Bowlsnapper/BSX-Mini/Photos/Hand Front.jpg

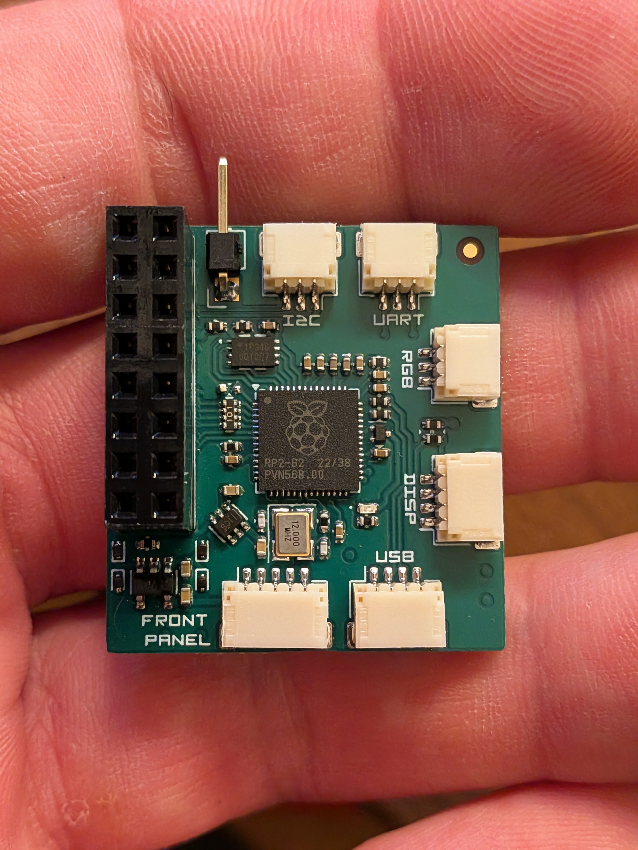
Photos/Hand Front.jpg
