Bowlsnapper/BSX-Mini/Photos/Pasted PCB 1.jpg

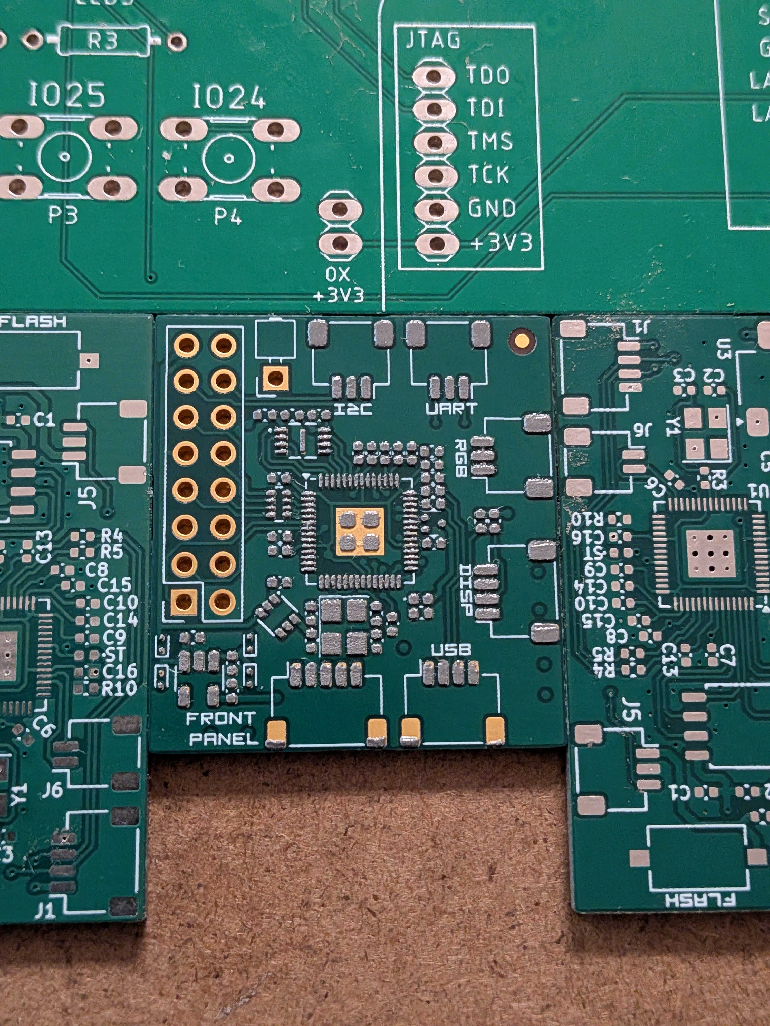
Photos/Pasted PCB 1.jpg
