Bowlsnapper/BSX-Mini/Theming/PrometheOS Skin/backgrounds/background.png

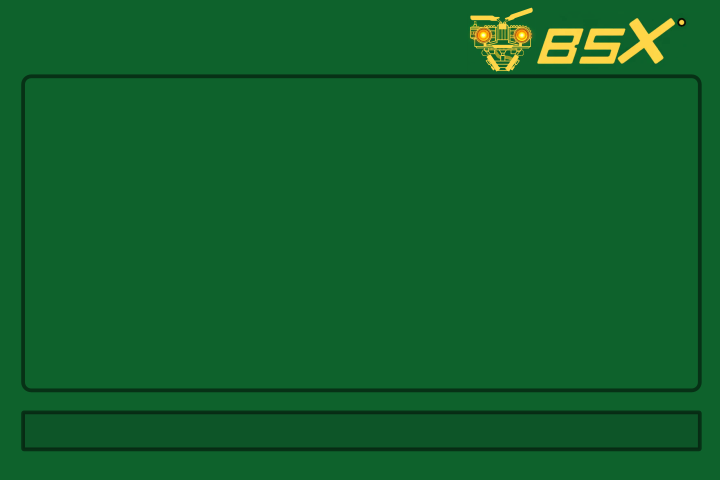
Theming/PrometheOS Skin/backgrounds/background.png
