Bowlsnapper/BSX-Mini/Photos/Assembly 2.jpg

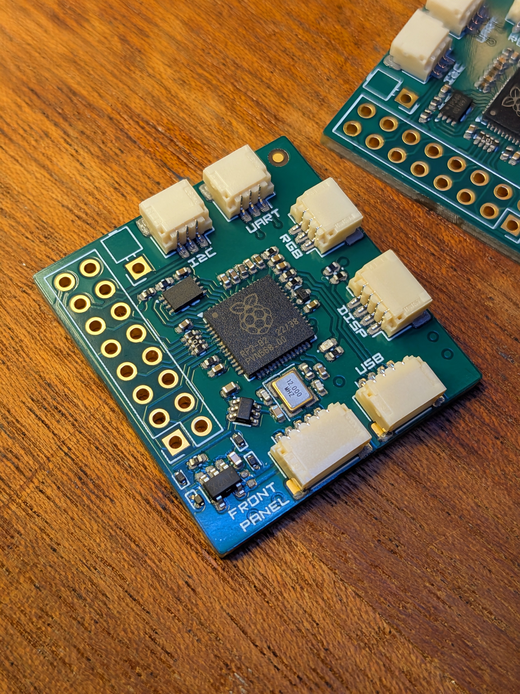
Photos/Assembly 2.jpg
